DptHiggs/Interferometry-CAD-Files/RENDERS/LI0001-CASE BODY.png

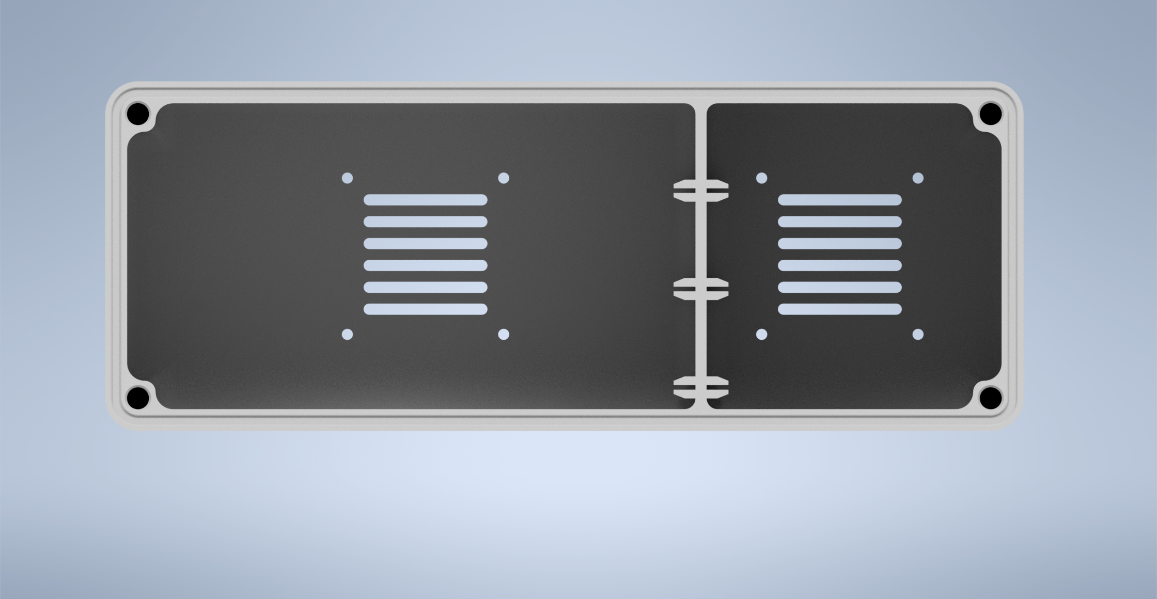
RENDERS/LI0001-CASE BODY.png
