DptHiggs/Interferometry-CAD-Files/RENDERS/LI0002-CASE LID.png

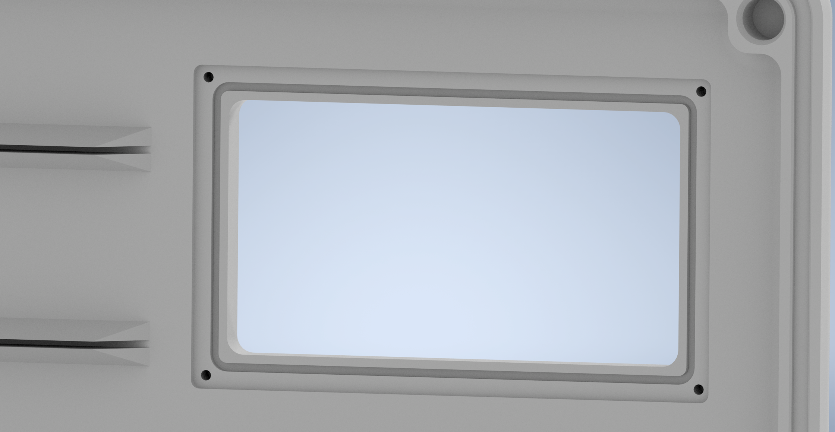
RENDERS/LI0002-CASE LID.png
