DptHiggs/Interferometry-CAD-Files/RENDERS/LIA0003-CASE ASSY 2.png

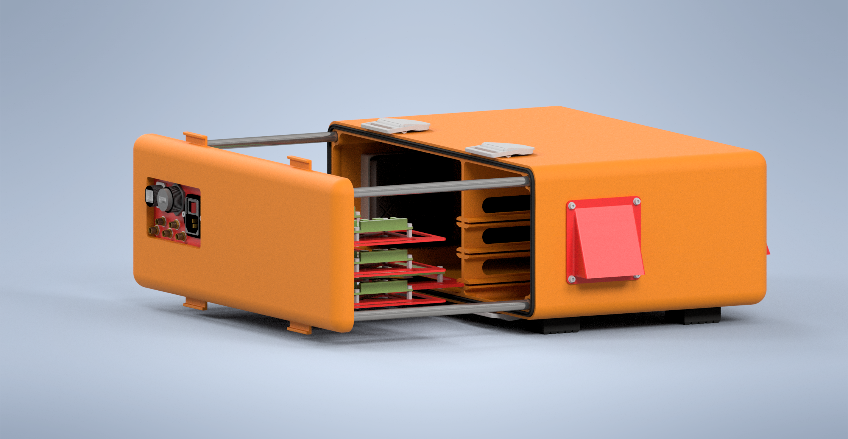
RENDERS/LIA0003-CASE ASSY 2.png
