DptHiggs/Interferometry-CAD-Files/RENDERS/LIA0003-CASE ASSY FAN COVERS.png

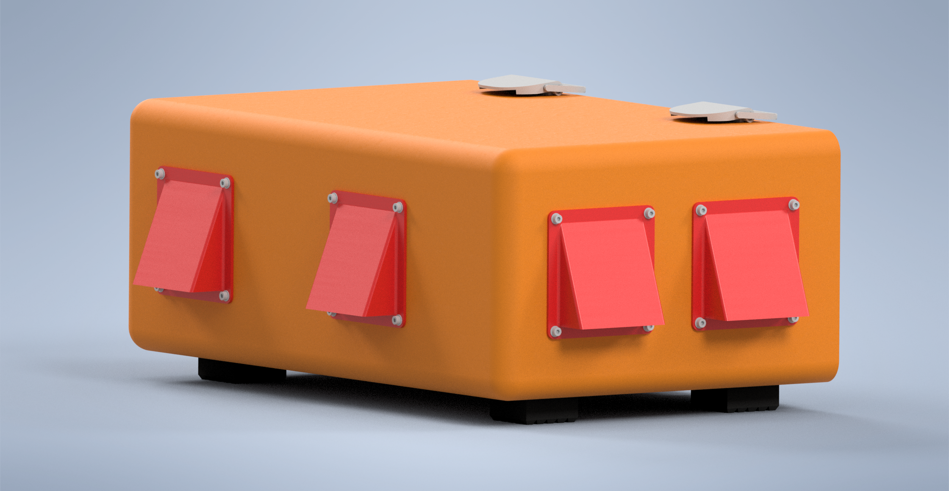
RENDERS/LIA0003-CASE ASSY FAN COVERS.png
