DptHiggs/Interferometry-CAD-Files/RENDERS/LIA0003-CASE ASSY SEAL.png

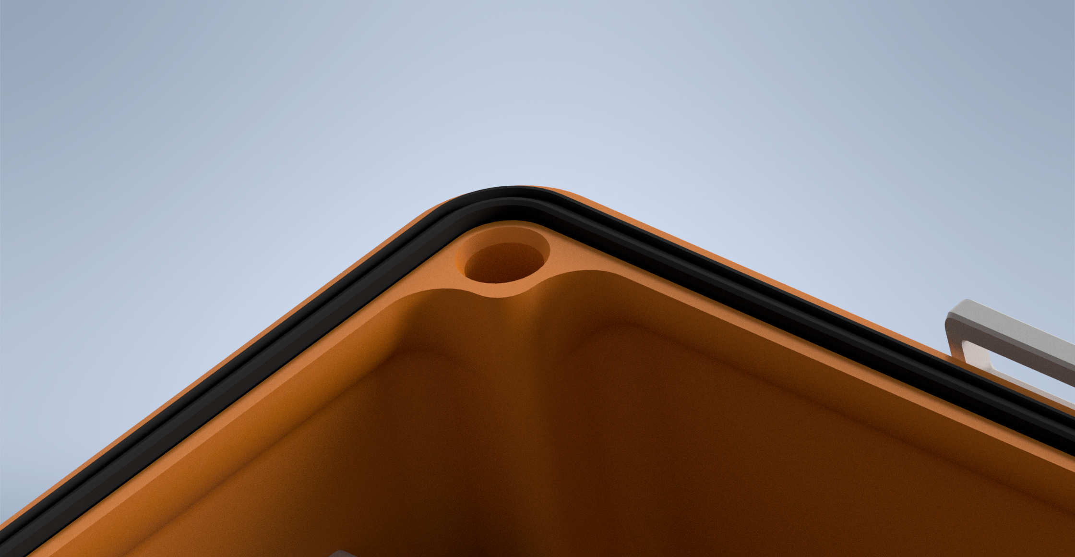
RENDERS/LIA0003-CASE ASSY SEAL.png
