DptHiggs/Interferometry-CAD-Files/SIMULATIONS/CFD/CFD3/Screenshot 2023-05-09 125852.png

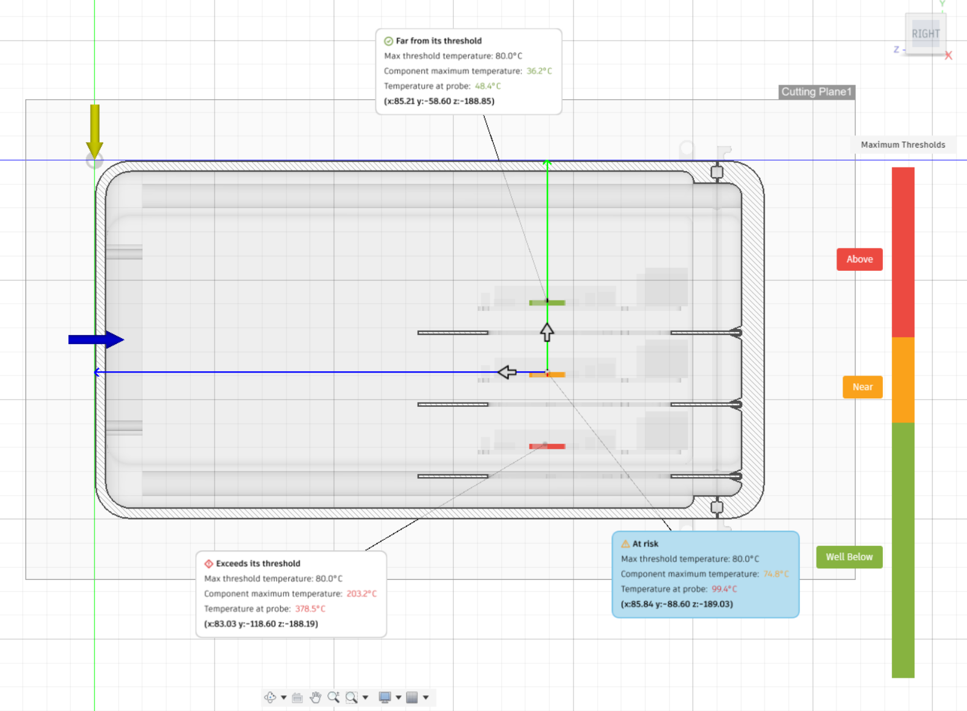
SIMULATIONS/CFD/CFD3/Screenshot 2023-05-09 125852.png
