DptHiggs/Interferometry-CAD-Files/SIMULATIONS/CFD/CFD 1/Screenshot 2023-05-08 135725.png

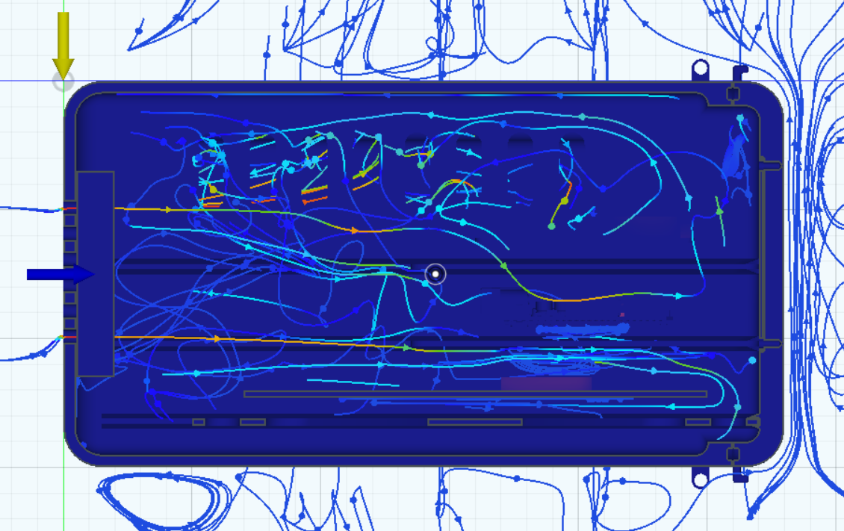
SIMULATIONS/CFD/CFD 1/Screenshot 2023-05-08 135725.png
