DptHiggs/Interferometry-CAD-Files/SIMULATIONS/CFD/CFD 2/Screenshot 2023-05-08 212548.png

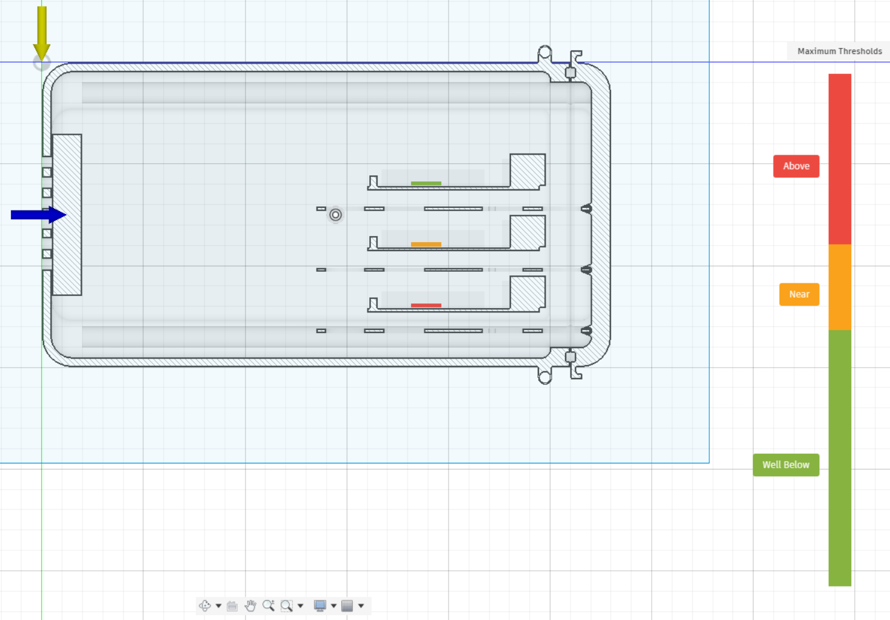
SIMULATIONS/CFD/CFD 2/Screenshot 2023-05-08 212548.png
