DptHiggs/Interferometry-CAD-Files/SIMULATIONS/CFD/CFD 2/Screenshot 2023-05-08 212629.png

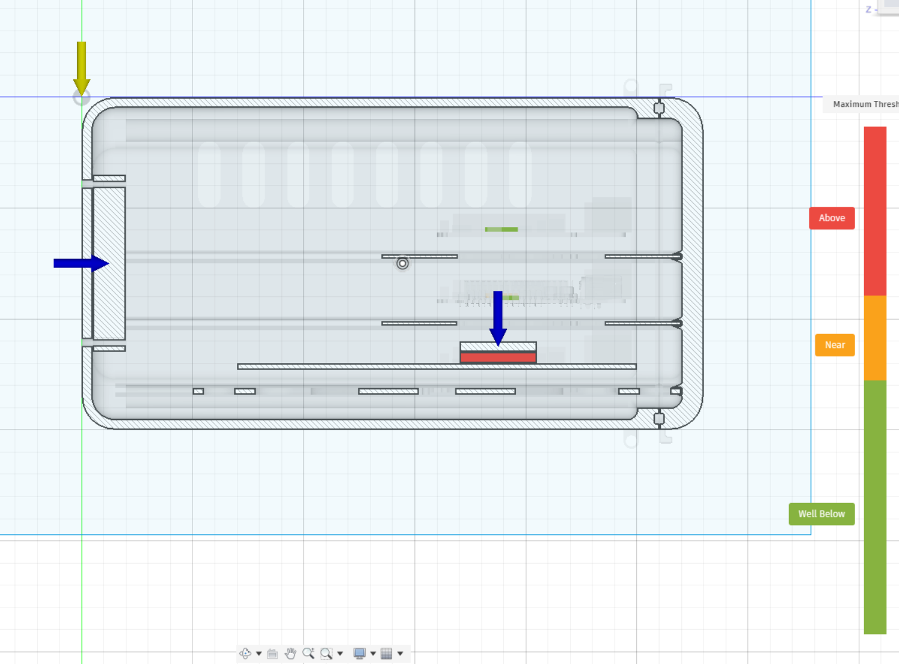
SIMULATIONS/CFD/CFD 2/Screenshot 2023-05-08 212629.png
