DptHiggs/Interferometry-CAD-Files/SIMULATIONS/CFD/CFD 4/Screenshot 2023-05-09 153237.png

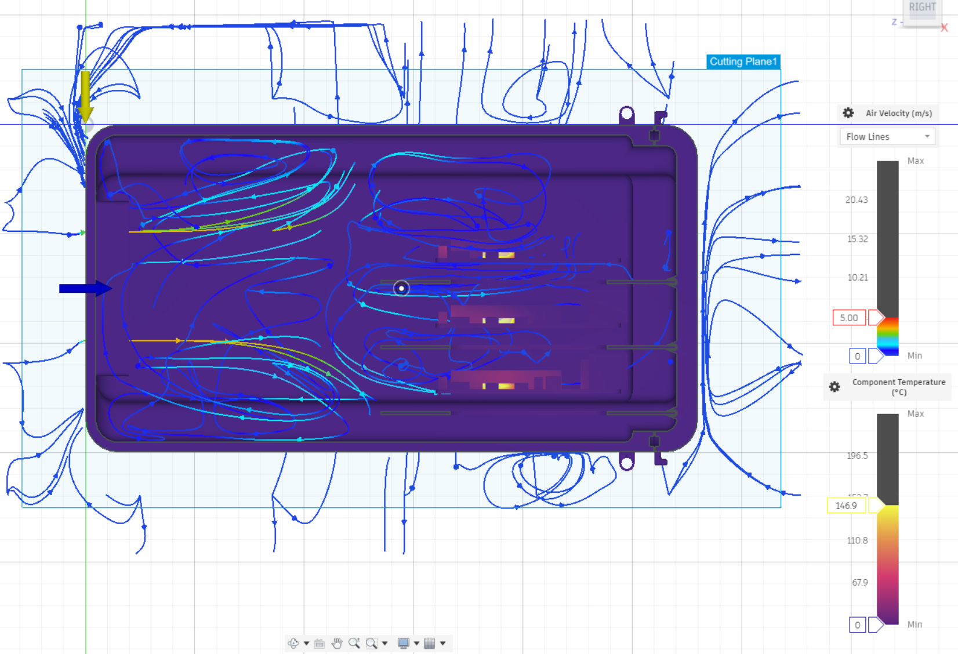
SIMULATIONS/CFD/CFD 4/Screenshot 2023-05-09 153237.png
