DptHiggs/Interferometry-CAD-Files/SIMULATIONS/CFD/CFD 5/Screenshot 2023-05-10 121610.png

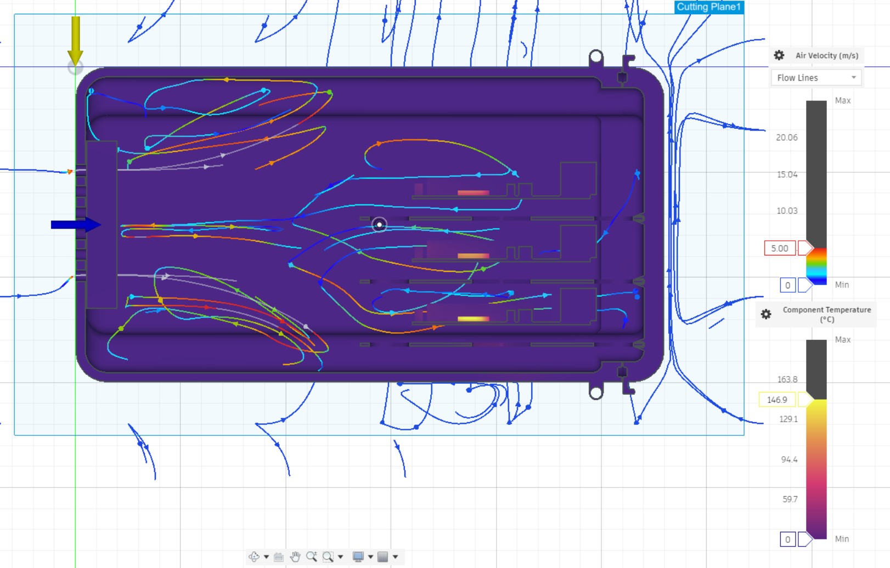
SIMULATIONS/CFD/CFD 5/Screenshot 2023-05-10 121610.png
