DptHiggs/Interferometry-CAD-Files/SIMULATIONS/CFD/CFD 6/Screenshot 2023-05-10 171933.png

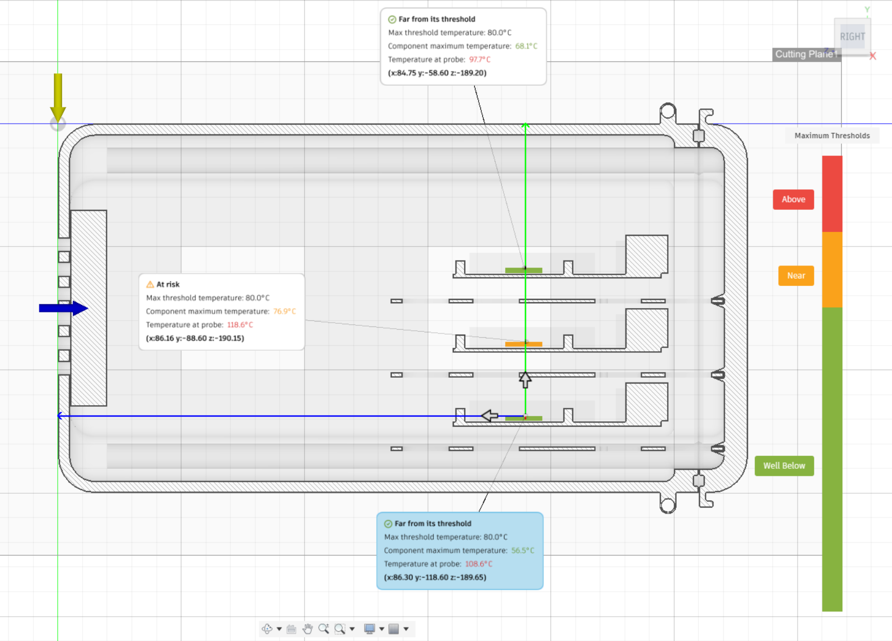
SIMULATIONS/CFD/CFD 6/Screenshot 2023-05-10 171933.png
