DptHiggs/Interferometry-CAD-Files/SIMULATIONS/CFD/CFD 7/Screenshot 2023-05-10 222111.png

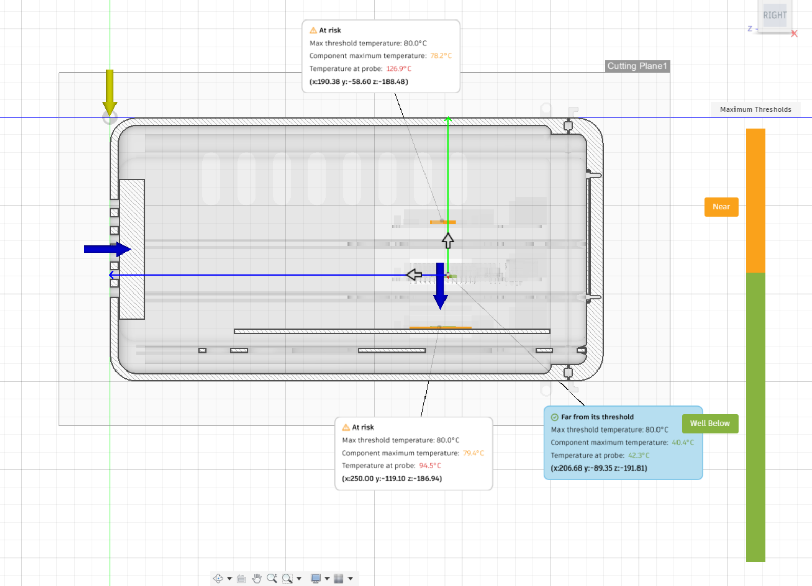
SIMULATIONS/CFD/CFD 7/Screenshot 2023-05-10 222111.png
