DptHiggs/Interferometry-CAD-Files/SIMULATIONS/CFD/CFD 7/Screenshot 2023-05-10 222427.png

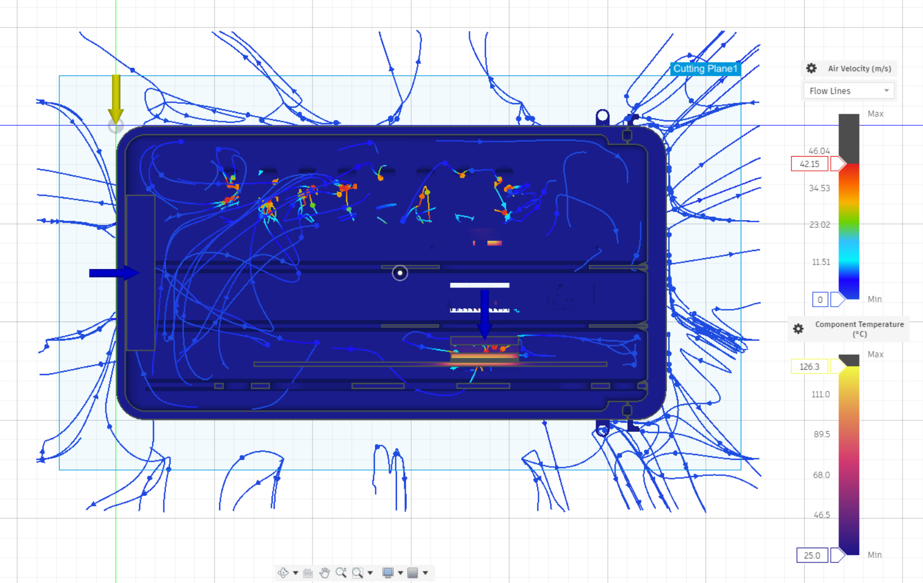
SIMULATIONS/CFD/CFD 7/Screenshot 2023-05-10 222427.png
