DptHiggs/Interferometry-CAD-Files/SIMULATIONS/FEA/ENCLOSURE/FEA 1/Screenshot 2023-05-11 110018.png

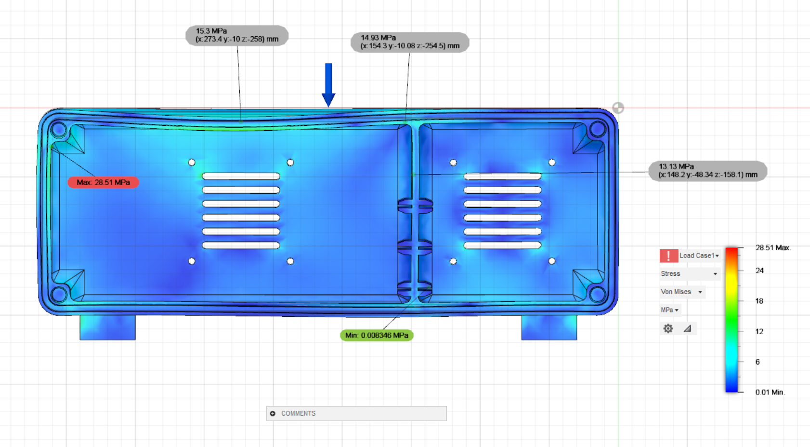
SIMULATIONS/FEA/ENCLOSURE/FEA 1/Screenshot 2023-05-11 110018.png
