DptHiggs/Interferometry-CAD-Files/SIMULATIONS/FEA/ENCLOSURE/FEA 2/Screenshot 2023-05-11 111324.png

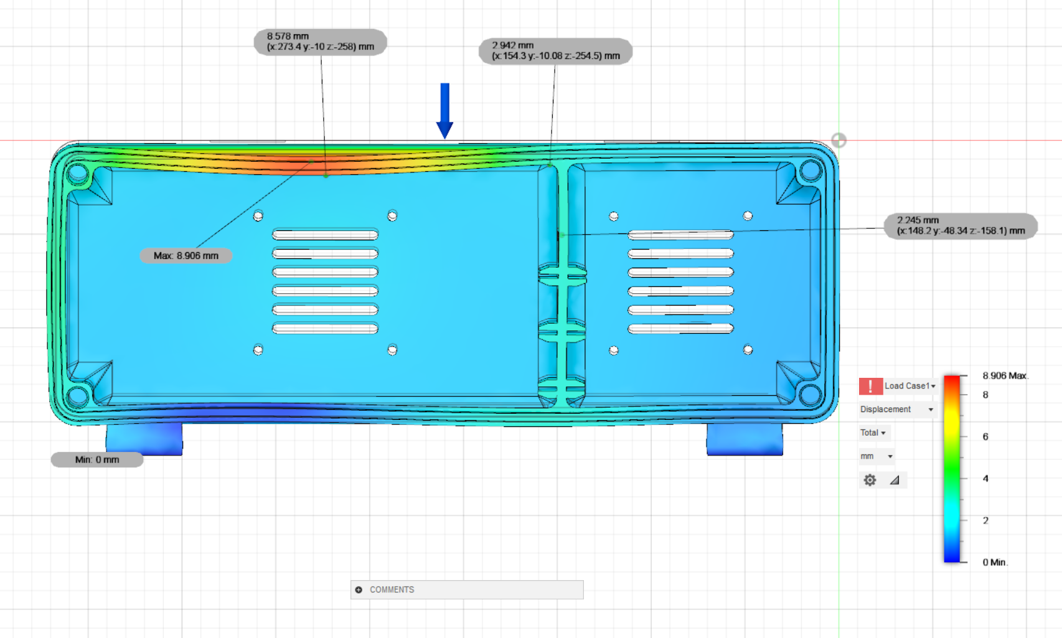
SIMULATIONS/FEA/ENCLOSURE/FEA 2/Screenshot 2023-05-11 111324.png
