DptHiggs/Interferometry-CAD-Files/SIMULATIONS/FEA/ENCLOSURE/FEA 3/Screenshot 2023-05-11 130657.png

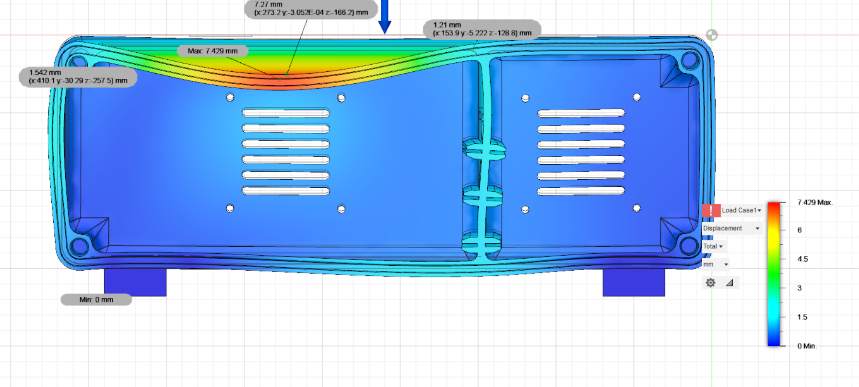
SIMULATIONS/FEA/ENCLOSURE/FEA 3/Screenshot 2023-05-11 130657.png
