DptHiggs/Interferometry-CAD-Files/SIMULATIONS/FEA/FPGA SHELF/SHELF 1/Screenshot 2023-05-15 172611.png

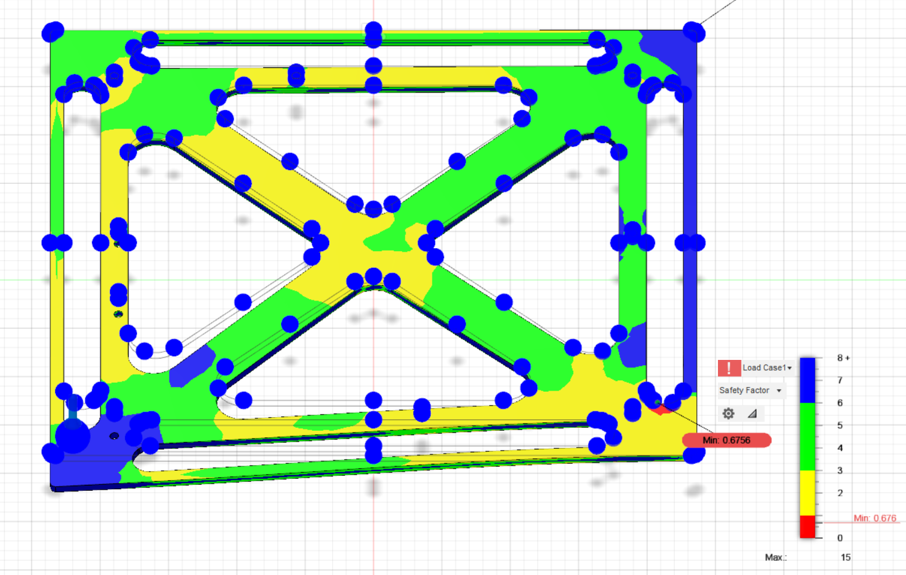
SIMULATIONS/FEA/FPGA SHELF/SHELF 1/Screenshot 2023-05-15 172611.png
