DptHiggs/Interferometry-CAD-Files/SIMULATIONS/FEA/FPGA SHELF/SHELF 2/Screenshot 2023-05-17 131416.png

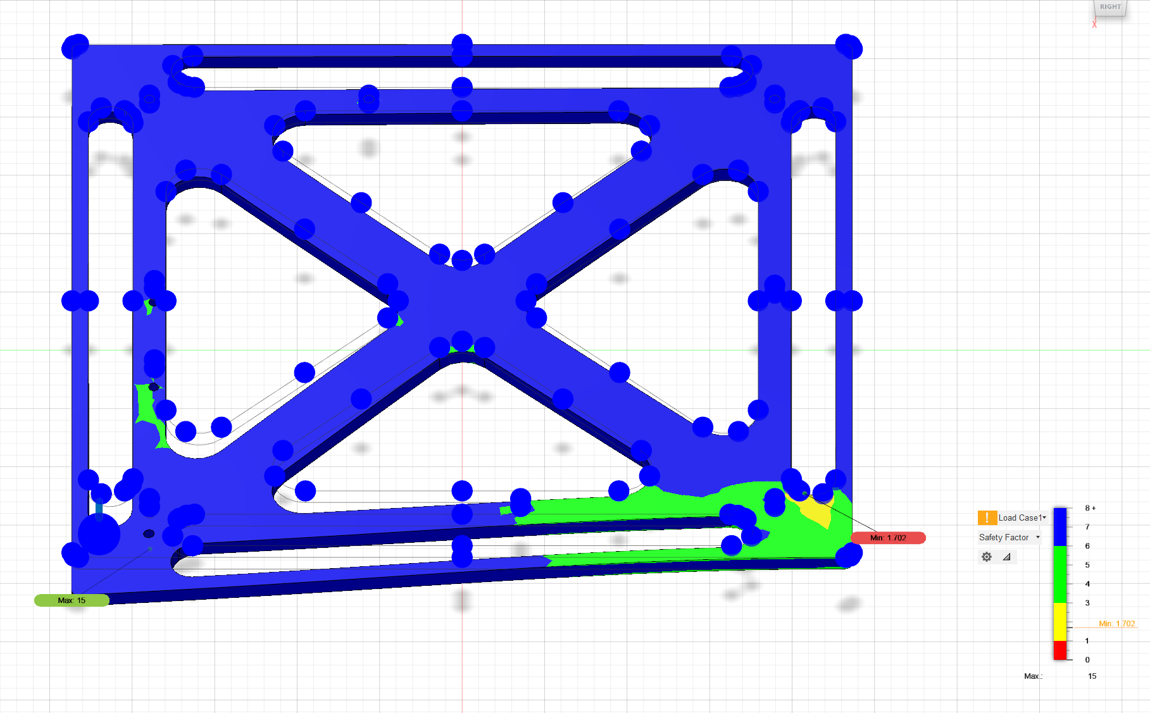
SIMULATIONS/FEA/FPGA SHELF/SHELF 2/Screenshot 2023-05-17 131416.png
