DptHiggs/Interferometry-CAD-Files/SIMULATIONS/FEA/FPGA SHELF/SHELF 3/Screenshot 2023-05-17 131902.png

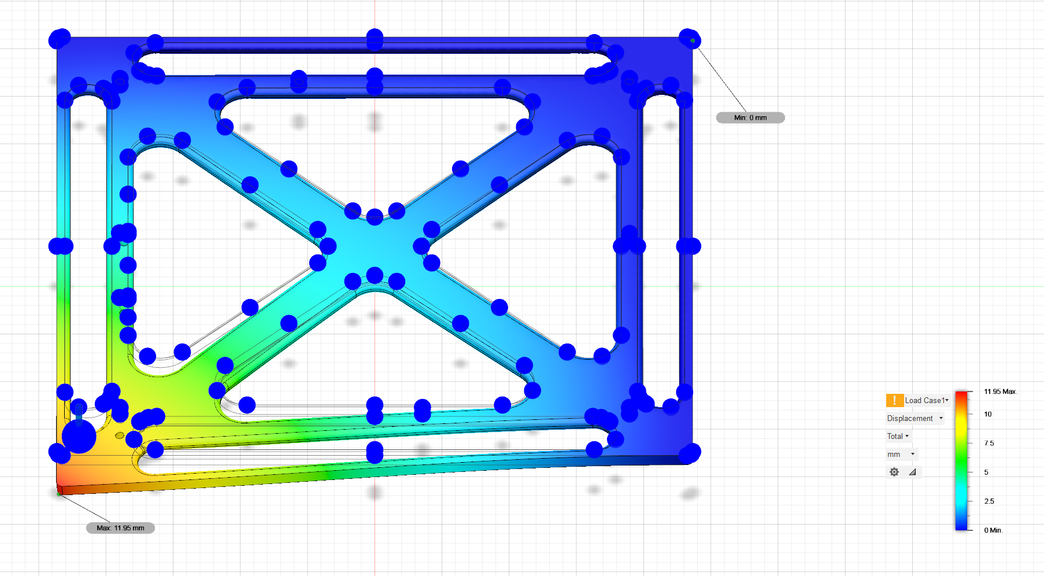
SIMULATIONS/FEA/FPGA SHELF/SHELF 3/Screenshot 2023-05-17 131902.png
