DptHiggs/Interferometry-CAD-Files/SIMULATIONS/FEA/FPGA SHELF/SHELF 4/Screenshot 2023-05-17 141246.png

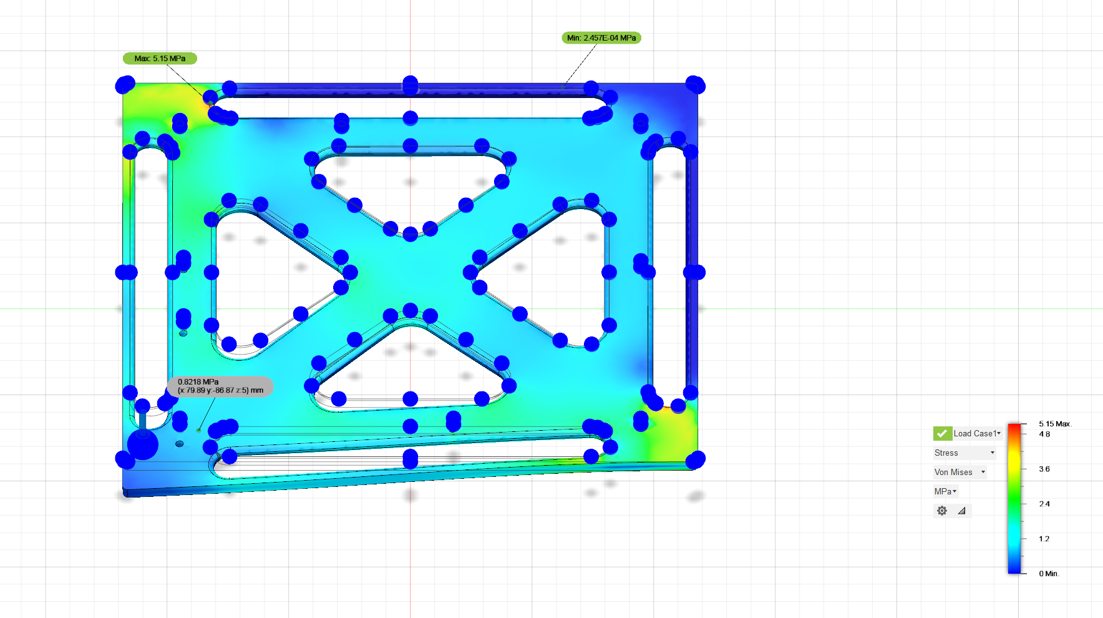
SIMULATIONS/FEA/FPGA SHELF/SHELF 4/Screenshot 2023-05-17 141246.png
