DptHiggs/Interferometry-CAD-Files/SIMULATIONS/FEA/COMPONENT SHELF/COMPONENT SHELF 1/Screenshot 2023-05-17 140248.png

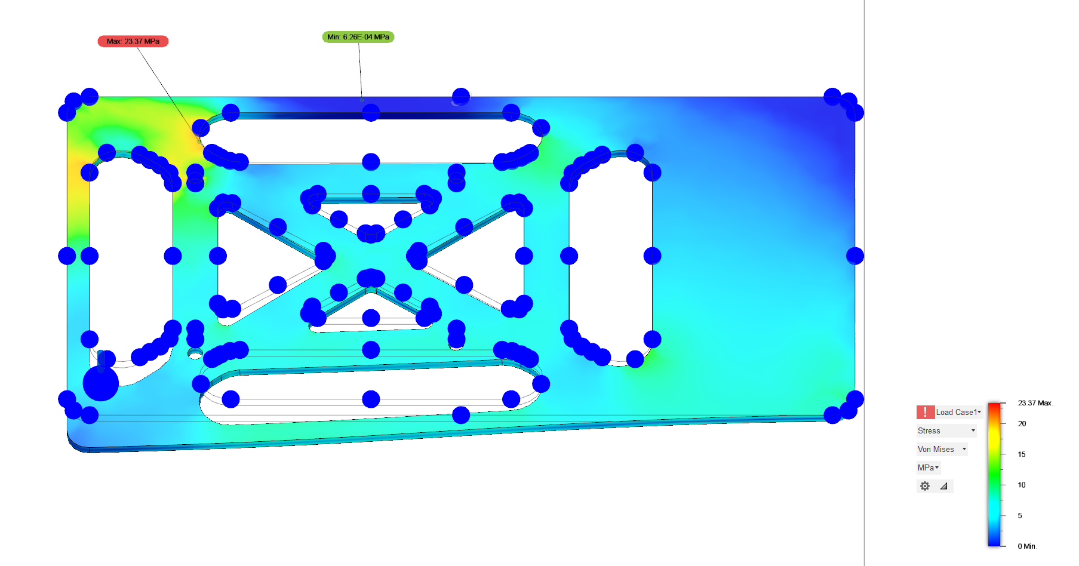
SIMULATIONS/FEA/COMPONENT SHELF/COMPONENT SHELF 1/Screenshot 2023-05-17 140248.png
