DptHiggs/Interferometry-CAD-Files/SIMULATIONS/FEA/COMPONENT SHELF/COMPONENT SHELF 2/Screenshot 2023-05-17 142109.png

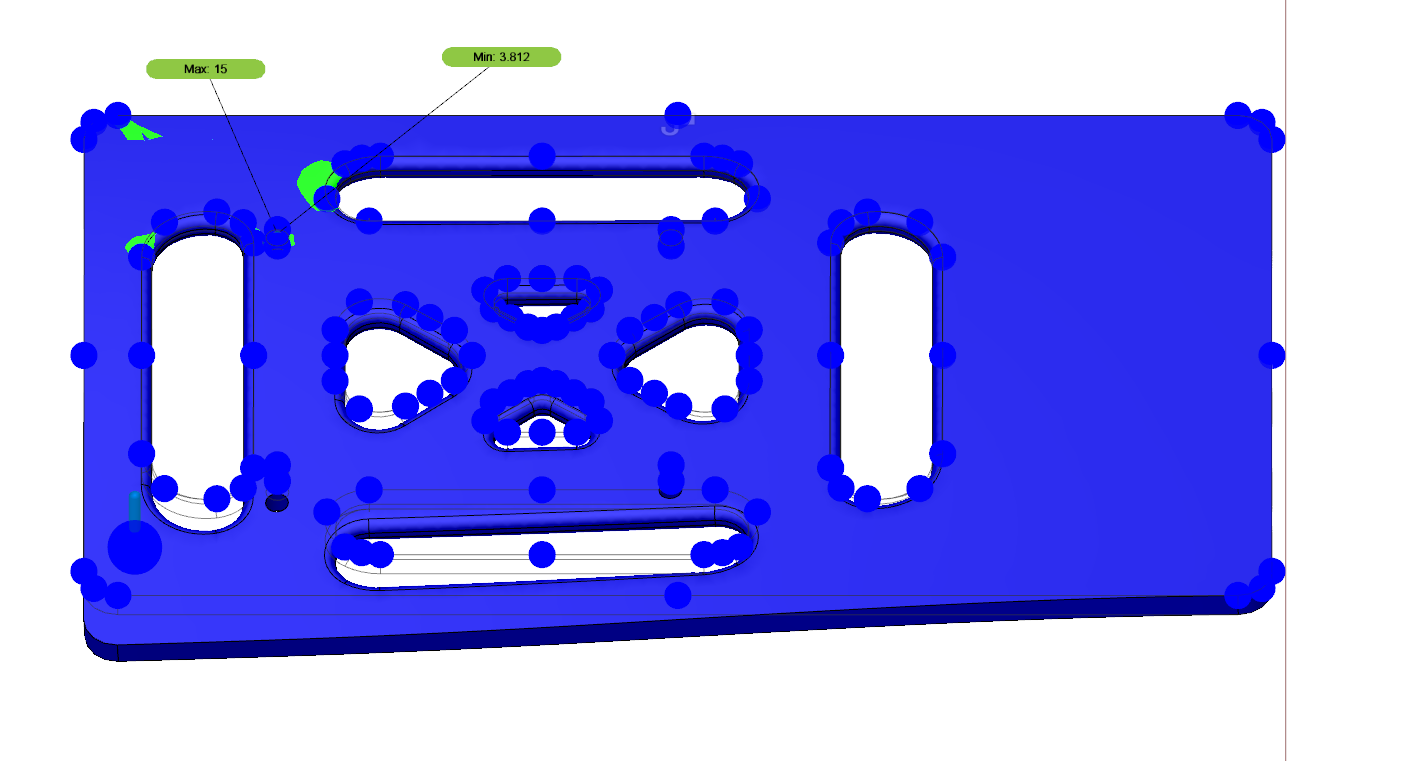
SIMULATIONS/FEA/COMPONENT SHELF/COMPONENT SHELF 2/Screenshot 2023-05-17 142109.png
